jeattine/Aquarium-Monitor/images/ConditionalTempDetect.png

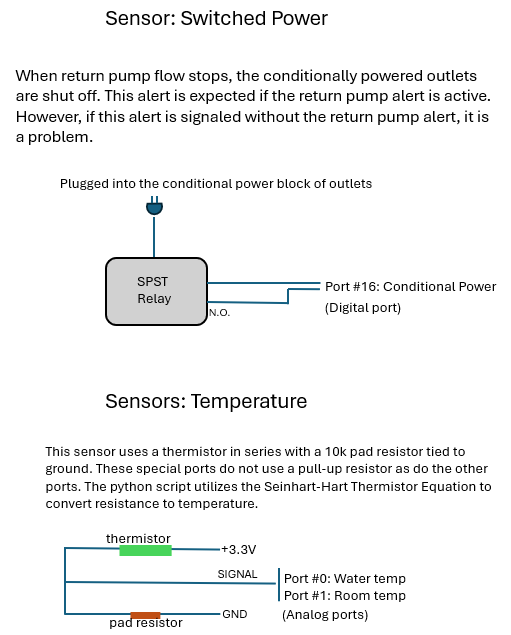
images/ConditionalTempDetect.png
