jeattine/Aquarium-Monitor/images/Controllers.jpg

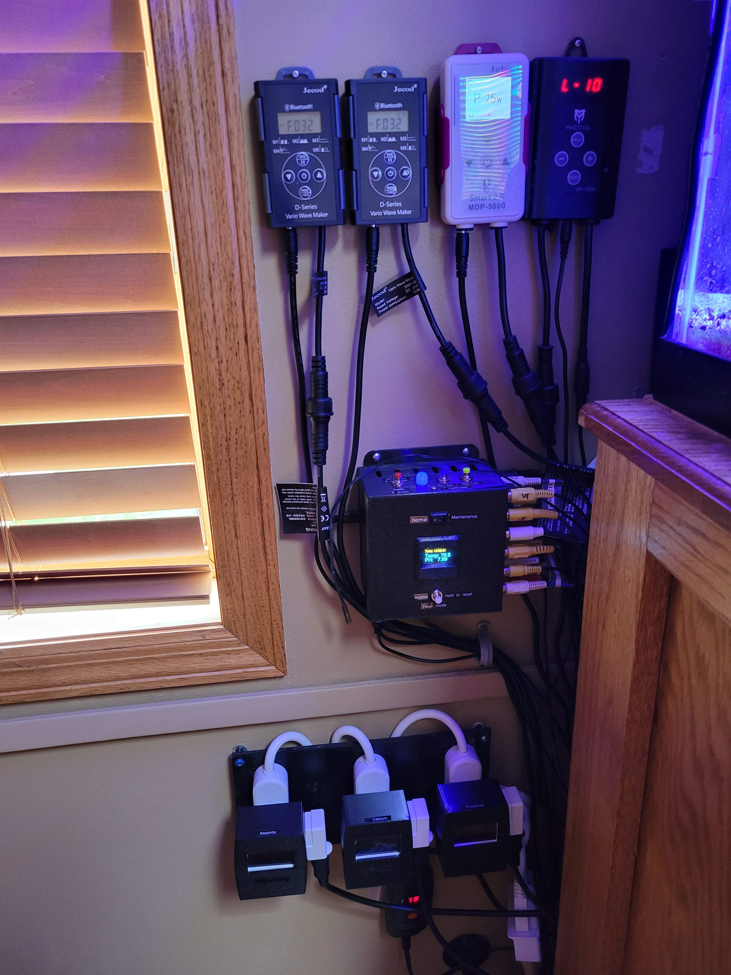
images/Controllers.jpg
