jeattine/Aquarium-Monitor/images/DisableBoot.png

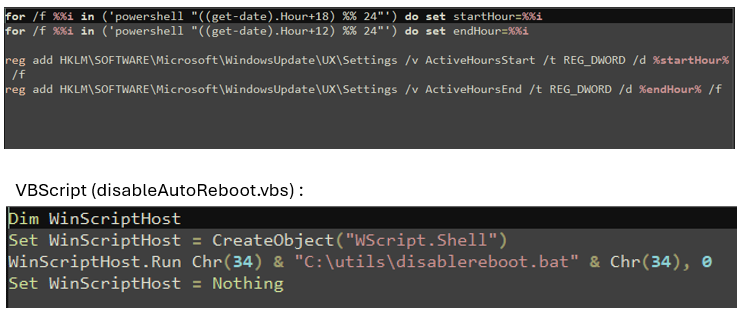
images/DisableBoot.png
