jeattine/Aquarium-Monitor/images/DisableReboot_ps1.png

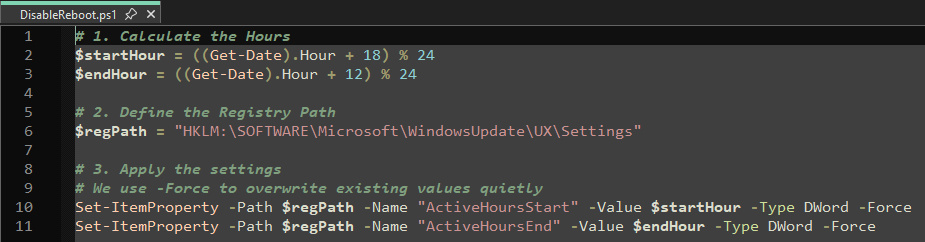
images/DisableReboot_ps1.png
