jeattine/Aquarium-Monitor/images/MonitorAttributes.png

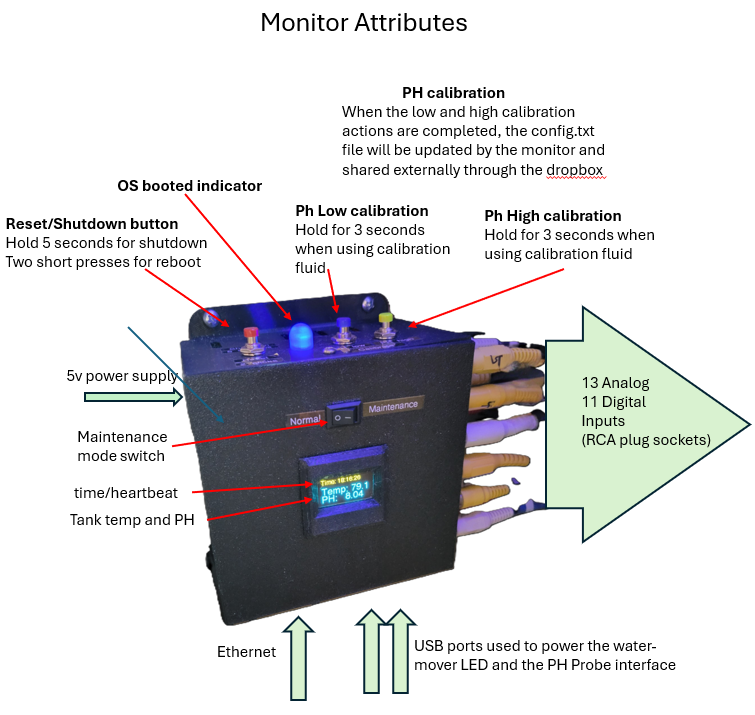
images/MonitorAttributes.png
