jeattine/Aquarium-Monitor/images/OutsideAir1.jpg

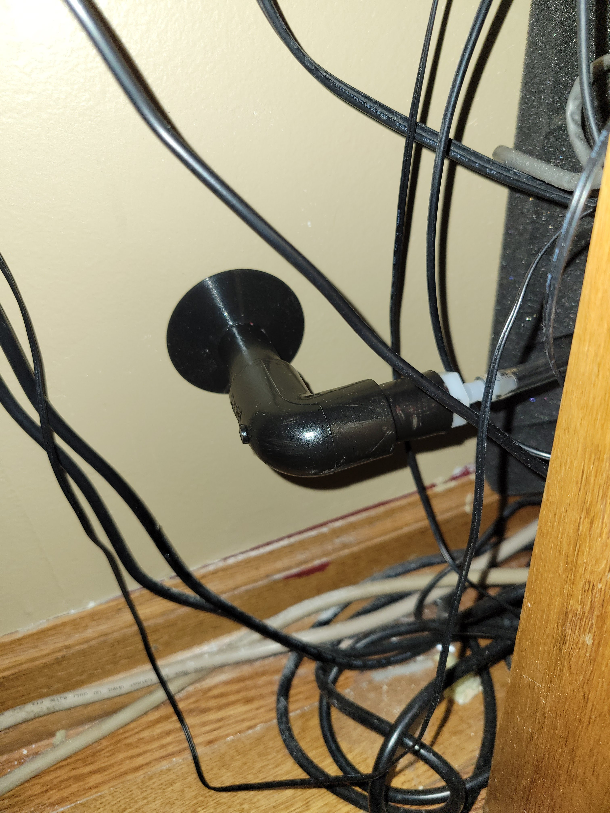
images/OutsideAir1.jpg
