jeattine/Aquarium-Monitor/images/OutsideAir2.jpg

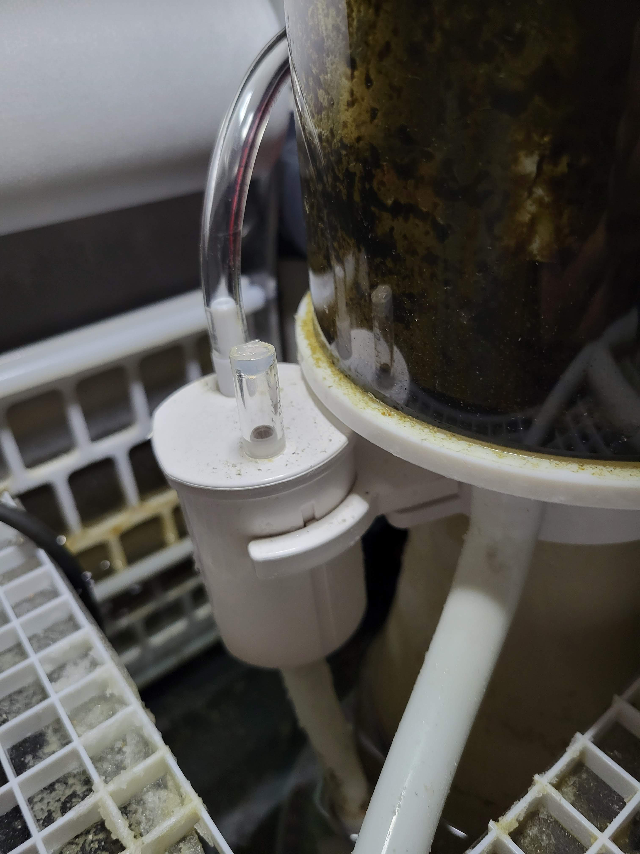
images/OutsideAir2.jpg
