jeattine/Aquarium-Monitor/images/Ph2Detect.png

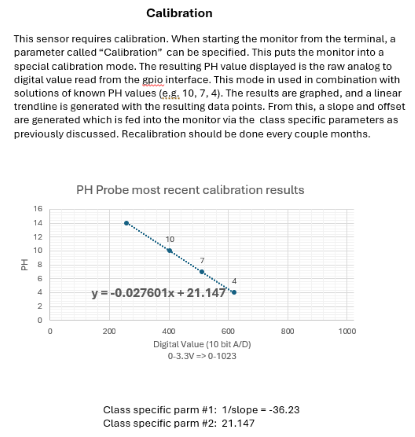
images/Ph2Detect.png
