jeattine/Aquarium-Monitor/images/PhDetect.png

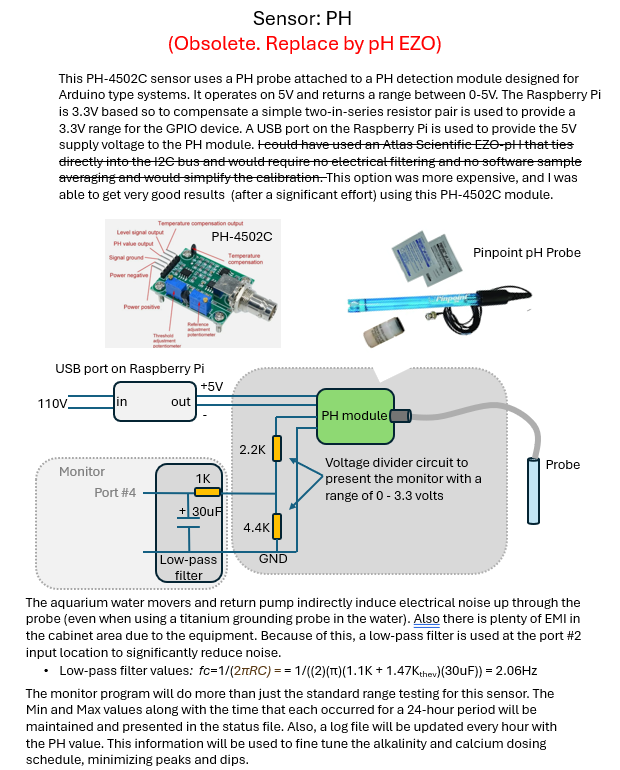
images/PhDetect.png
