jeattine/Aquarium-Monitor/images/Resilience.png

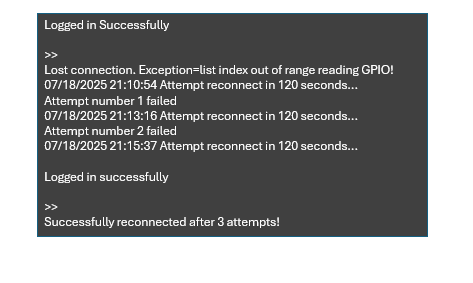
images/Resilience.png
