jeattine/Aquarium-Monitor/images/SystemView.png

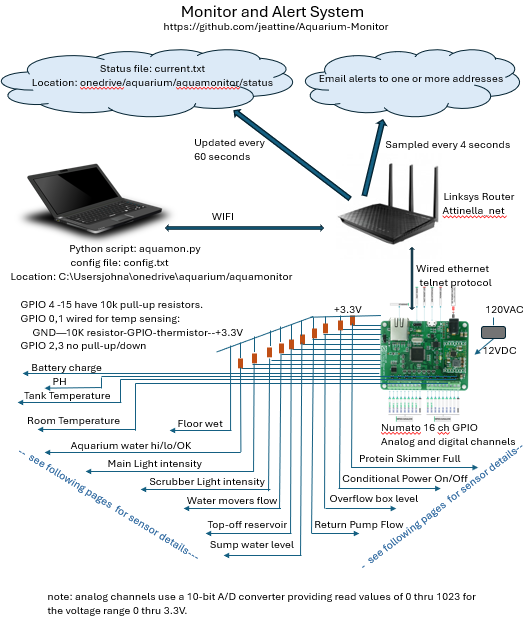
images/SystemView.png
