jeattine/Aquarium-Monitor/images/TaskScheduler2.png

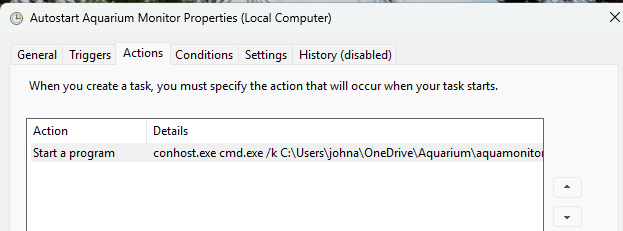
images/TaskScheduler2.png
