jeattine/Aquarium-Monitor/images/TaskScheduler3.png

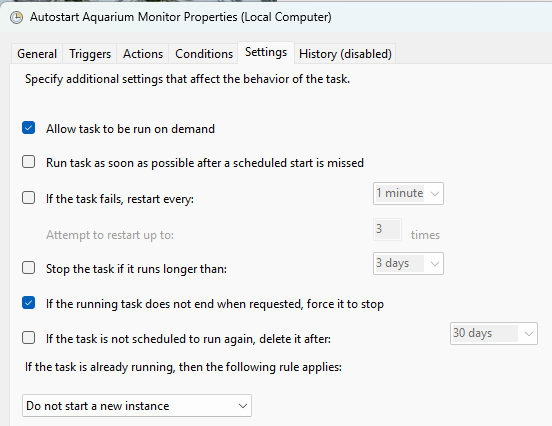
images/TaskScheduler3.png
