jeattine/Aquarium-Monitor/images/TaskScheduler4.png

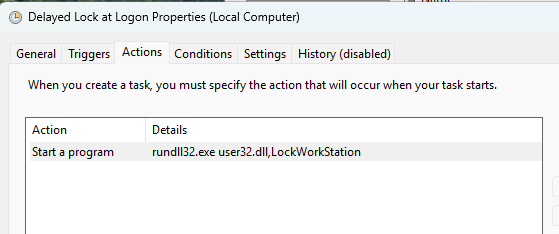
images/TaskScheduler4.png
