jeattine/Aquarium-Monitor/images/TaskScheduler5.png

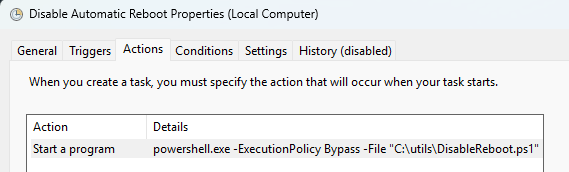
images/TaskScheduler5.png
