jeattine/Aquarium-Monitor/images/VariousDetect.png

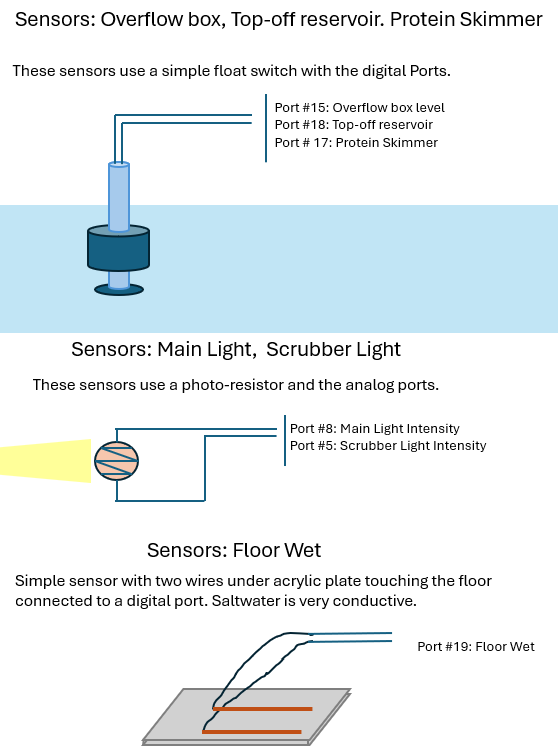
images/VariousDetect.png
