jeattine/Aquarium-Monitor/Print3D/Pin40Standoff.FCStd

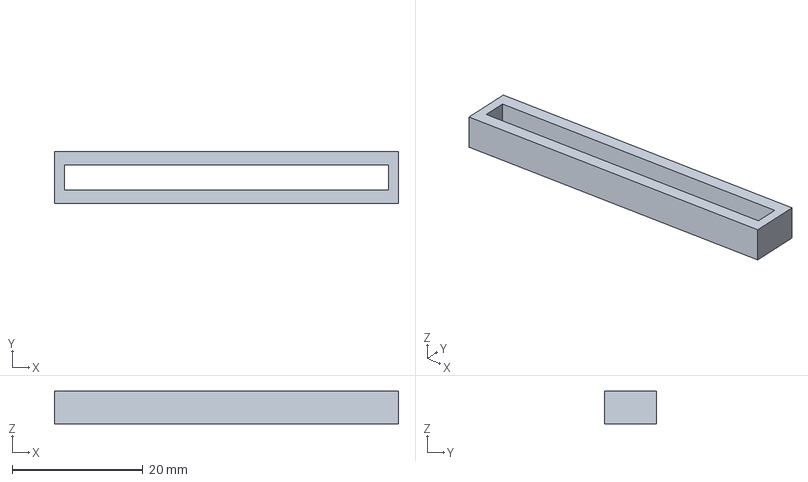
[picture p57: CAD file, 2026-02-24]
Print3D/Pin40Standoff.FCStd
52.6 x 8.00 x 5.00 mm
