jeattine/Aquarium-Monitor/Print3D/MonitorPlugPlate.FCStd

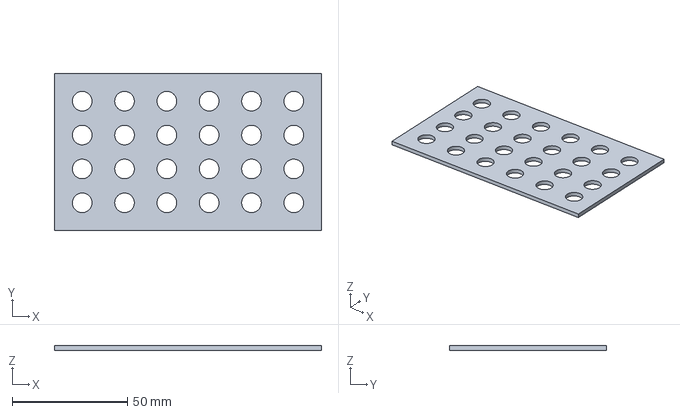
[picture p58: CAD file, 2026-02-24]
Print3D/MonitorPlugPlate.FCStd
115.6 x 68.0 x 2.00 mm
