jeattine/Aquarium-Monitor/Print3D/MonitorEnclosure.FCStd

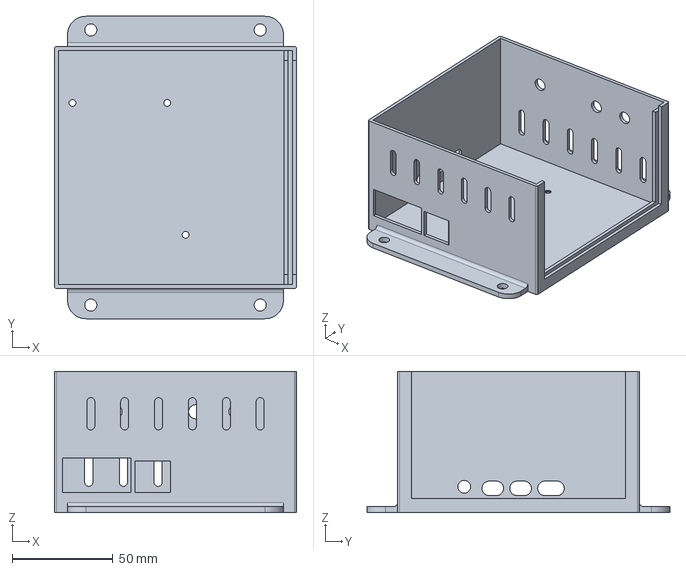
[picture p59: CAD file, 2026-02-24]
Print3D/MonitorEnclosure.FCStd
120.0 x 150.0 x 70.0 mm
