jeattine/Aquarium-Monitor/images/scrubber1.jpg

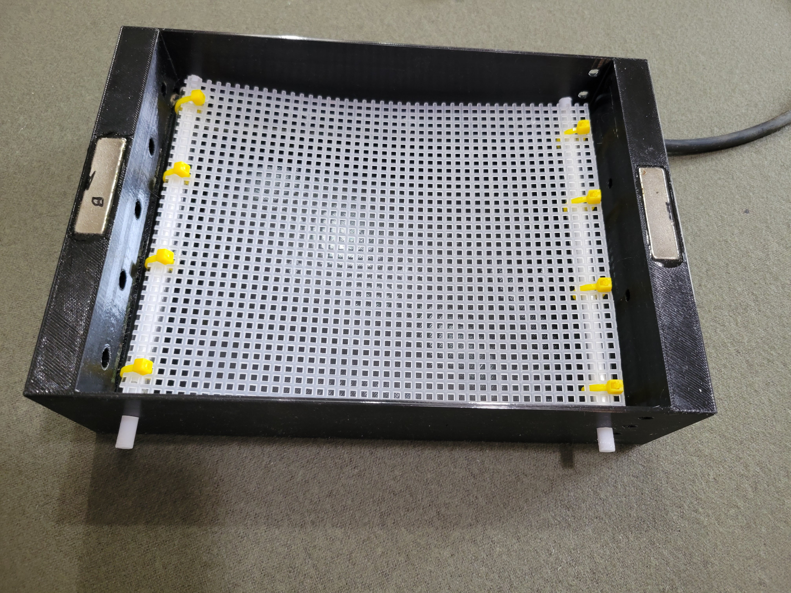
images/scrubber1.jpg
